HolyErgo/DES-MX-low-profile/openscad/make_right.scad

use <generator.scad>

// Generates all keycaps for right part
generate_part(right);
