HolyErgo/DES-MX-low-profile/openscad/make_test.scad

use <generator.scad>

// Generates all keycaps for test part
generate_part(test);
